lunikodevelopment/dell-optiplex-7450-full-case/generated/h2c/front_bottom_left.step

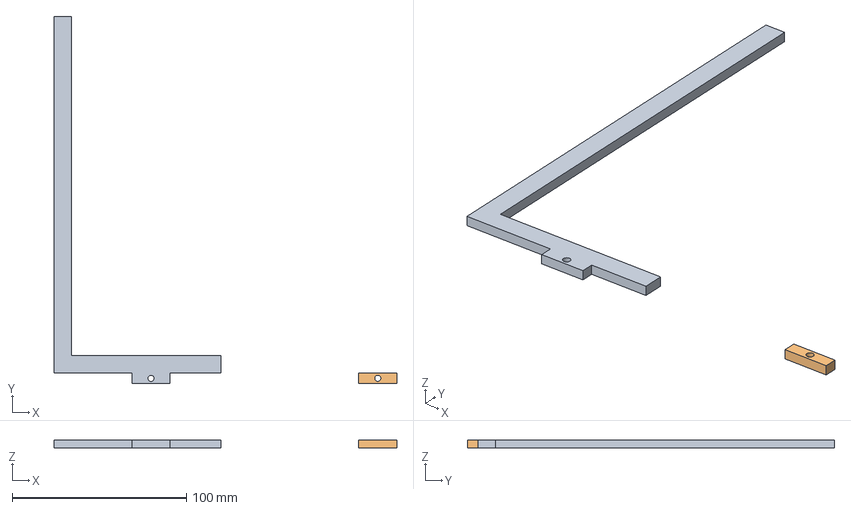
[picture p15: CAD file, 2026-08-09]
generated/h2c/front_bottom_left.step
196.6 x 210.4 x 4.50 mm
