lunikodevelopment/dell-optiplex-7450-full-case/generated/universal/vesa_receiver_128x128_10mm.step

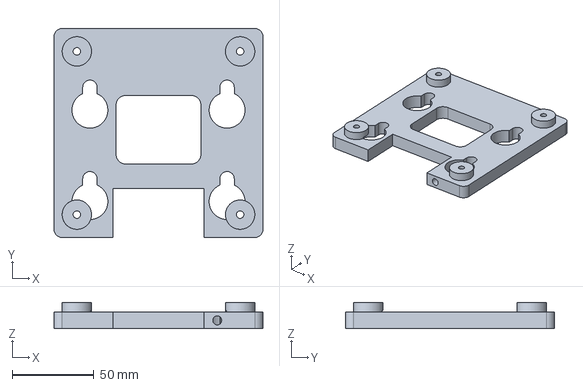
[picture p16: CAD file, 2026-08-09]
generated/universal/vesa_receiver_128x128_10mm.step
128.0 x 128.0 x 16.0 mm
