lunikodevelopment/dell-optiplex-7450-full-case/generated/fit_checks/enclosure_front_corner_coupon.step

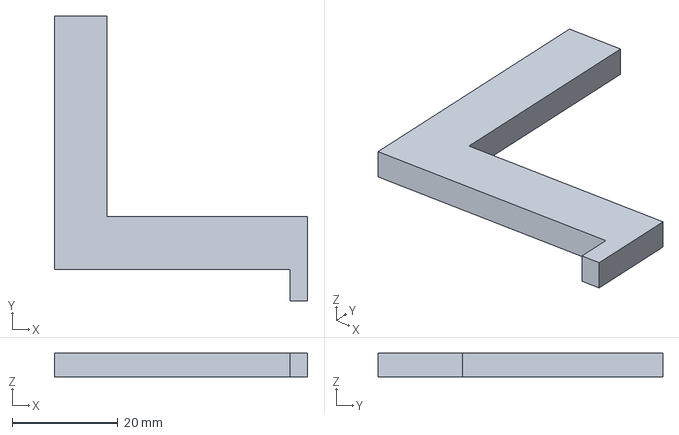
[picture p17: CAD file, 2026-08-09]
generated/fit_checks/enclosure_front_corner_coupon.step
48.0 x 54.0 x 4.50 mm
