lunikodevelopment/dell-optiplex-7450-full-case/generated/universal/positive_anti_lift_lock_block.step

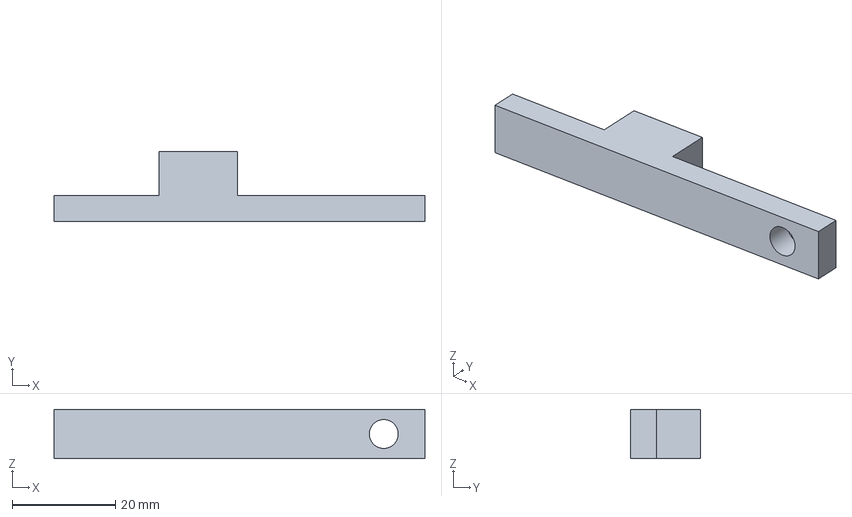
[picture p18: CAD file, 2026-08-09]
generated/universal/positive_anti_lift_lock_block.step
72.0 x 13.5 x 9.60 mm
