lunikodevelopment/dell-optiplex-7450-full-case/generated/h2c/front_top_left.step

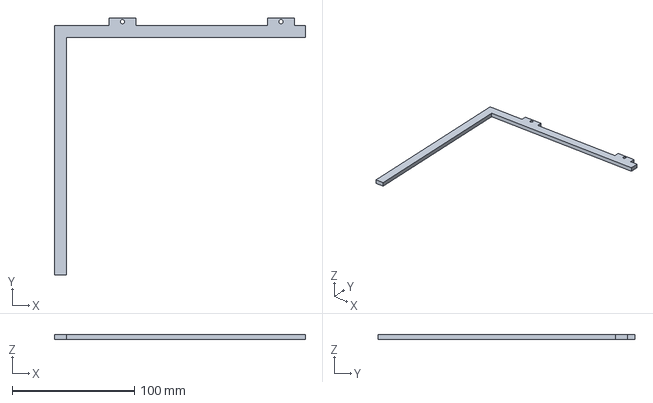
[picture p20: CAD file, 2026-08-09]
generated/h2c/front_top_left.step
205.6 x 210.4 x 4.50 mm
