lunikodevelopment/dell-optiplex-7450-full-case/generated/universal/wall_plate_4xM8_stud.step

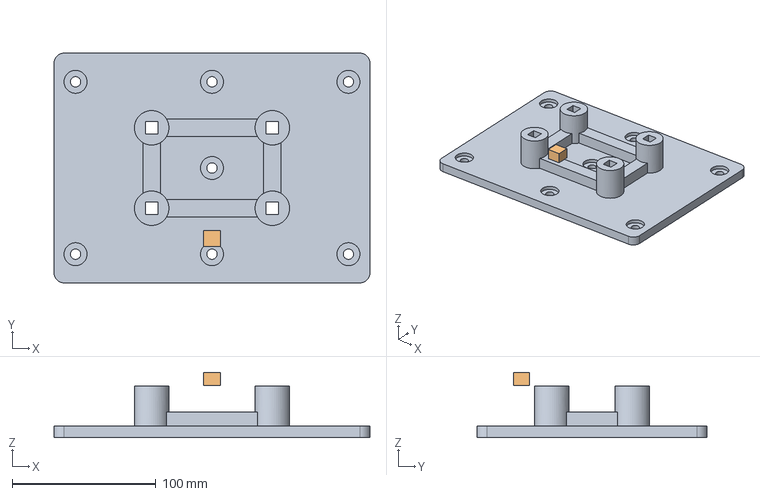
[picture p21: CAD file, 2026-08-09]
generated/universal/wall_plate_4xM8_stud.step
220.0 x 160.0 x 45.4 mm
