lunikodevelopment/dell-optiplex-7450-full-case/generated/fit_checks/front_overlap_3_4_5mm_coupon.step

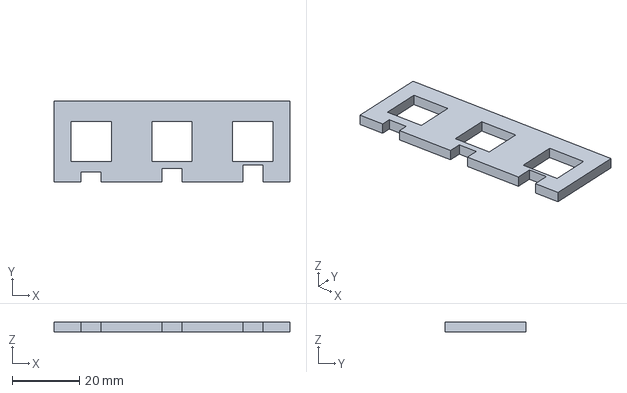
[picture p22: CAD file, 2026-08-09]
generated/fit_checks/front_overlap_3_4_5mm_coupon.step
70.0 x 24.0 x 3.00 mm
