lunikodevelopment/dell-optiplex-7450-full-case/generated/universal/seam_joiner_130mm.step

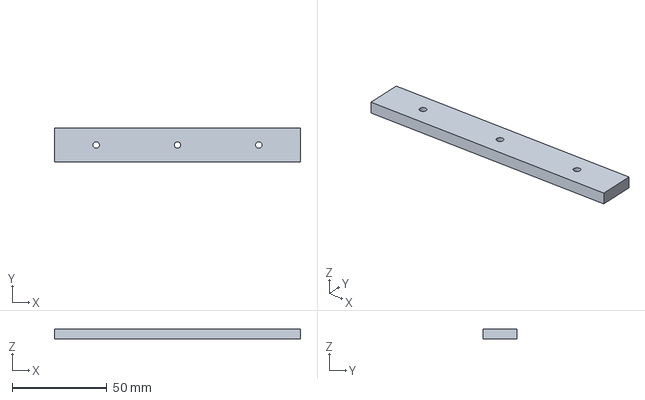
[picture p23: CAD file, 2026-08-09]
generated/universal/seam_joiner_130mm.step
130.0 x 18.0 x 5.50 mm
